eliachiarucci/DA15/Core/Inc/main.h

#define DAC_MUTE_Pin GPIO_PIN_0
#define DAC_MUTE_GPIO_Port GPIOA
#define CC2_V_Pin GPIO_PIN_0
#define CC2_V_GPIO_Port GPIOB
#define CC1_V_Pin GPIO_PIN_1
#define CC1_V_GPIO_Port GPIOB
#define AMP_EN_Pin GPIO_PIN_12
#define AMP_EN_GPIO_Port GPIOB
#define TRIM_A_Pin GPIO_PIN_14
#define TRIM_A_GPIO_Port GPIOB
#define TRIM_A_EXTI_IRQn EXTI14_IRQn
#define TRIM_B_Pin GPIO_PIN_15
#define TRIM_B_GPIO_Port GPIOB
#define TRIM_B_EXTI_IRQn EXTI15_IRQn
#define ENCODER_PUSH_I_Pin GPIO_PIN_8
#define ENCODER_PUSH_I_GPIO_Port GPIOA
