eliachiarucci/DA15/App/Inc/app.h

// SPDX-License-Identifier: GPL-3.0-only
// Copyright (c) 2026 Elia Chiarucci

#ifndef APP_H
#define APP_H

#include <stdint.h>

void app_init(void);
void app_loop(void);

// Returns power level: 0=500mA, 1=1500mA, 2=3000mA
uint8_t app_get_power_level(void);

// Reboot into STM32 system bootloader (USB DFU mode)
void app_reboot_to_dfu(void);

// Save current settings (volume, EQ, active profile, etc.) to flash immediately
void app_save_settings(void);

// Force the analog path silent (DAC mute + amp off) via direct register
// writes — safe to call from any fault handler context
void app_fault_safe_state(void);

#endif
